MachinesJesus/oslac/OSLAC_PCB/output/20190227_PCB_SAC_etch_silk_bottom.pdf

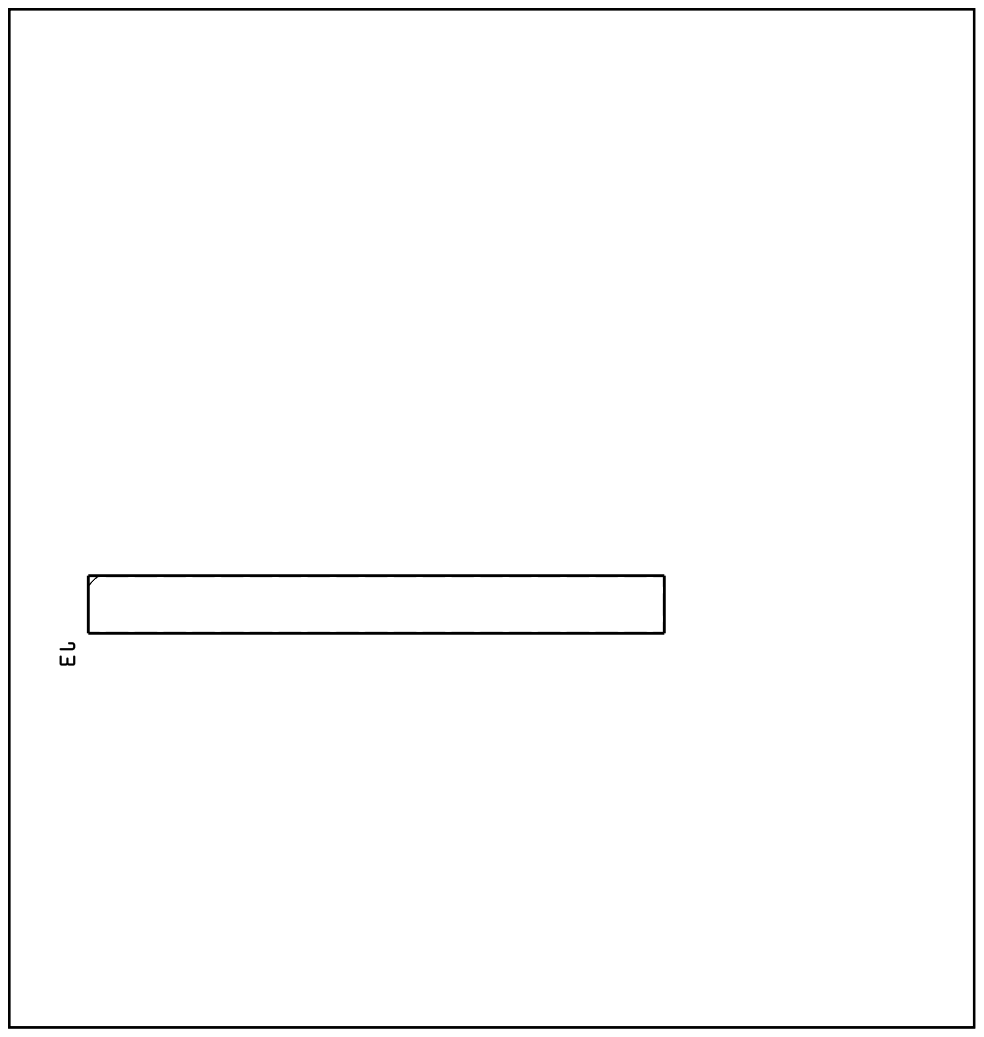
[picture p9: page 1]
