MachinesJesus/oslac/OSLAC_PCB/output/20190227_PCB_SAC_etch_silk_bottom_mirror.pdf

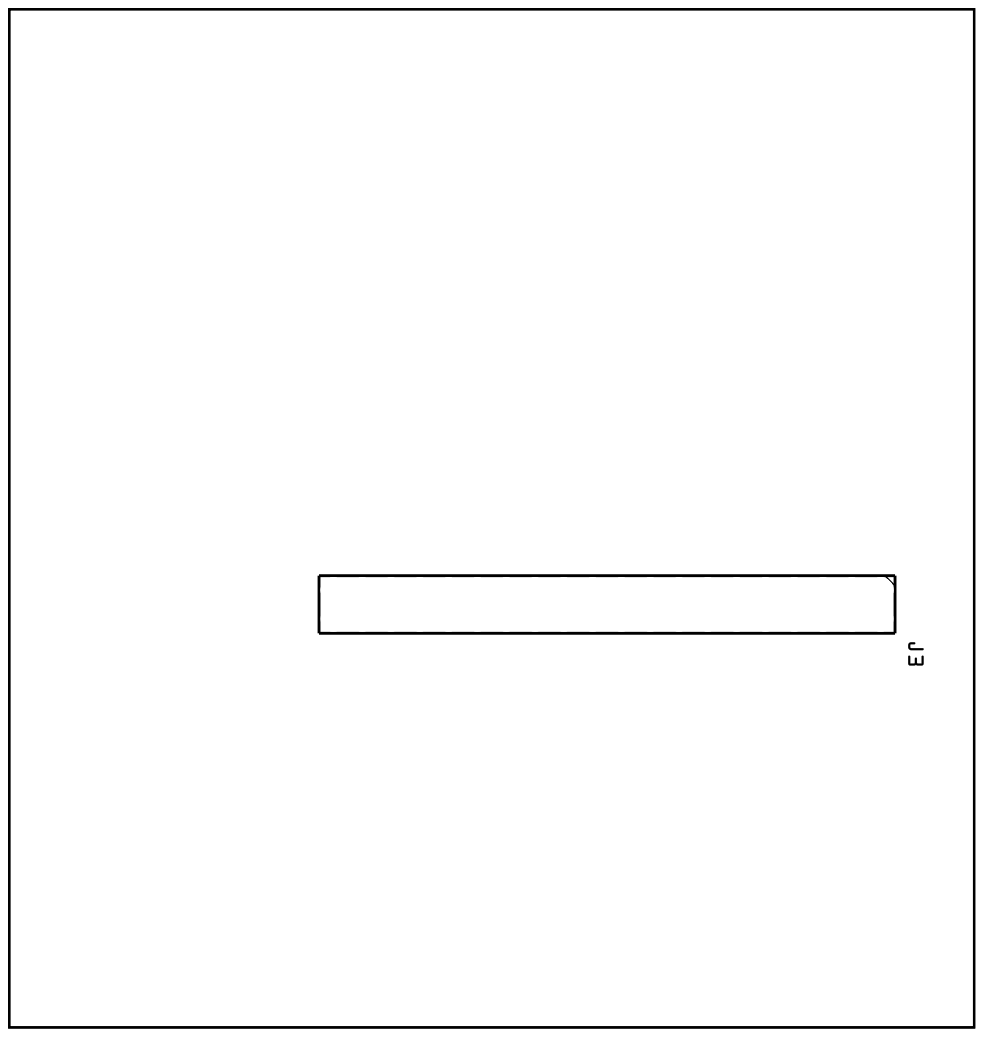
[picture p10: page 1]
