MachinesJesus/oslac/OSLAC_PCB/output/20190227_PCB_SAC_etch_silk_top.pdf

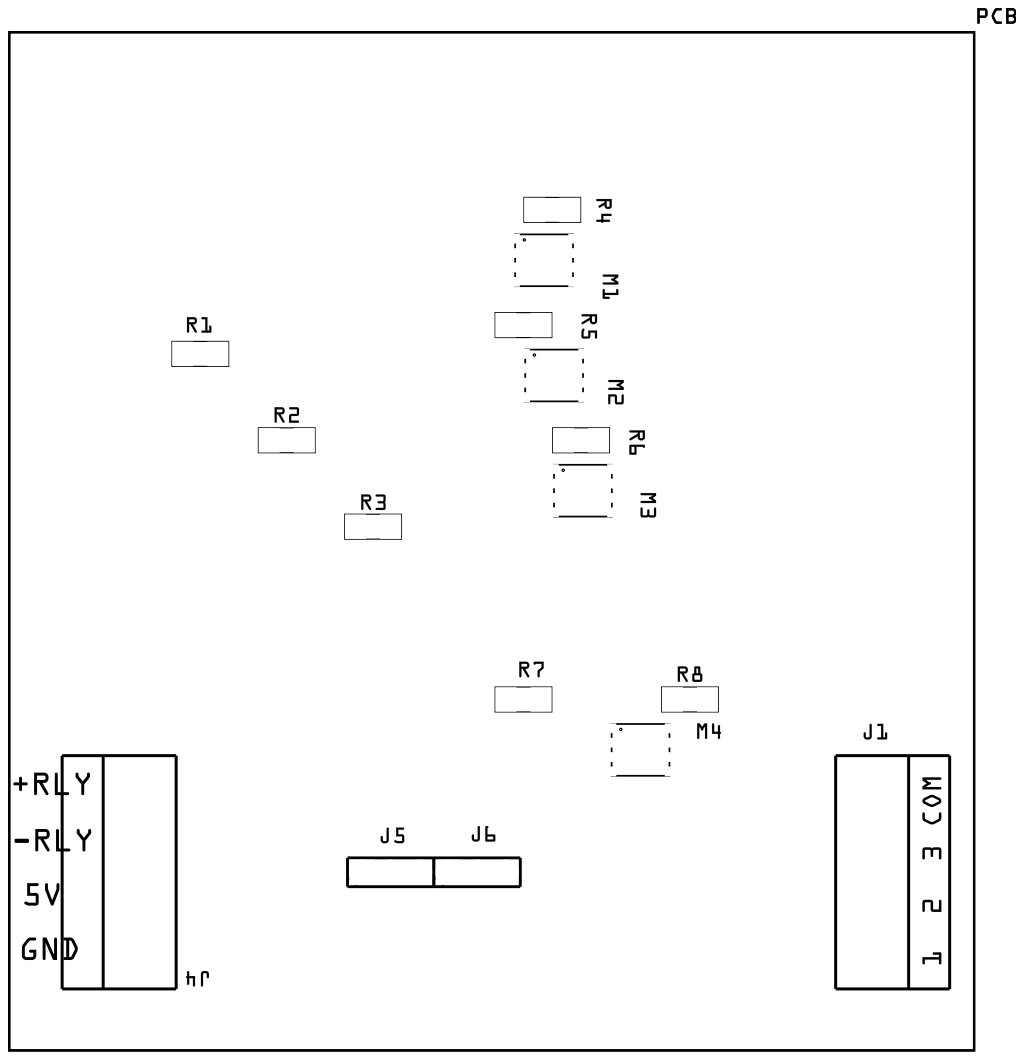
[picture p11: page 1]
