MachinesJesus/oslac/OSLAC_PCB/output/20190227_PCB_SAC_etch_silk_top_mirror.pdf

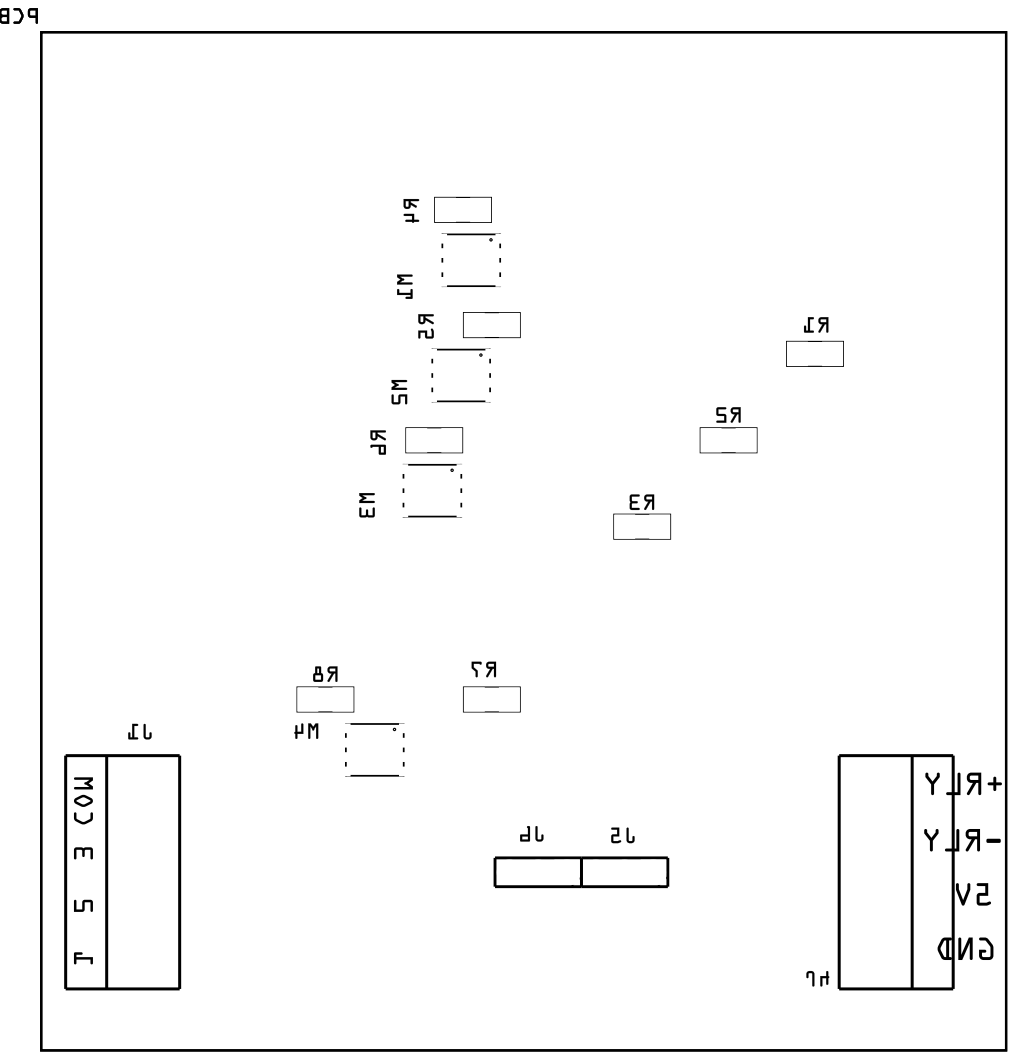
[picture p12: page 1]
